burningion/skate-judge/capture/onboard.py

#!/usr/bin/env python3
# /// script
# requires-python = ">=3.10"
# dependencies = ["pyserial>=3.5"]
# ///
"""Record motion on SD or ESP32 flash; download after recording stops.

python3 capture/onboard.py record
python3 capture/onboard.py list
python3 capture/onboard.py download ID --output sessions/recovered
"""

from __future__ import annotations

import argparse
import io
from datetime import datetime, timezone
from http.client import IncompleteRead
import json
import math
import os
from pathlib import Path
import queue
import re
import sys
import threading
import time
from urllib.error import HTTPError, URLError
from urllib.parse import urlencode, urlsplit
from urllib.request import Request, urlopen
import uuid
import zlib

if __package__:
    from .onboard_log import import_log, read_packets
    from .session import ControlServer, append_json
else:
    from onboard_log import import_log, read_packets
    from session import ControlServer, append_json


def valid_id(identity):
    if not isinstance(identity, str) or not re.fullmatch(r"[a-f0-9]{32}", identity):
        raise ValueError("Expected a 32-character recording ID from the board's file list.")
    return identity


def checksum(path):
    crc = 0
    with Path(path).open("rb") as stream:
        for chunk in iter(lambda: stream.read(65536), b""):
            crc = zlib.crc32(chunk, crc)
    return f"{crc:08x}"


class BoardClient:
    def __init__(self, address="http://192.168.4.1", opener=urlopen):
        if "://" not in address:
            address = "http://" + address
        parsed = urlsplit(address)
        if parsed.scheme != "http" or not parsed.hostname or parsed.username or parsed.query or parsed.fragment:
            raise ValueError("Use the board's HTTP address, for example http://192.168.4.1.")
        self.address = address.rstrip("/")
        self.opener = opener
        self.lock = threading.Lock()

    def close(self):
        pass

    def request(self, route, params=None, post=False, timeout=2):
        url = self.address + route + ("?" + urlencode(params) if params else "")
        request = Request(url, data=b"" if post else None, method="POST" if post else "GET")
        try:
            with self.lock, self.opener(request, timeout=timeout) as response:
                return json.load(response)
        except HTTPError as error:
            try:
                message = json.load(error).get("error", str(error))
            except (ValueError, AttributeError):
                message = str(error)
            raise ValueError(message) from error
        except (URLError, TimeoutError, OSError) as error:
            raise OSError(f"Board connection unavailable: {error}") from error

    def download(self, identity, directory, storage=None):
        identity = valid_id(identity)
        params = {"id": identity}
        if storage is not None:
            if storage not in ("sd", "flash"):
                raise ValueError("Storage must be sd or flash.")
            params["storage"] = storage
        info = self.request("/file-info", params, timeout=120)
        backend = info.get("storage")
        if storage is not None and backend is None:
            raise ValueError("Install updated firmware to select a storage backend explicitly.")
        if backend is not None:
            if backend not in ("sd", "flash") or (storage and storage != backend):
                raise ValueError("Invalid or changed storage backend from board.")
            params["storage"] = backend
        if info.get("id") != identity or not isinstance(info.get("bytes"), int) or info["bytes"] <= 0:
            raise ValueError("Invalid file metadata from board.")
        directory = Path(directory)
        directory.mkdir(parents=True, exist_ok=True)
        target = directory / f"onboard-{identity}.bin"
        partial = target.with_suffix(".bin.part")
        if target.exists():
            if target.stat().st_size != info["bytes"] or checksum(target) != info["crc32"]:
                raise ValueError("An existing download differs from the board; it will not be overwritten.")
            return target
        last_error = None
        for _ in range(3):
            offset = partial.stat().st_size if partial.exists() else 0
            if offset > info["bytes"]:
                raise ValueError("Partial file is larger than the board recording; keep it and use a new directory.")
            if offset == info["bytes"]:
                break
            url = self.address + "/file?" + urlencode(dict(params, offset=offset))
            try:
                with self.lock, self.opener(url, timeout=5) as response:
                    if response.headers.get("X-Log-CRC32") != info["crc32"]:
                        raise ValueError("Recording changed during download.")
                    with partial.open("ab") as stream:
                        remaining = info["bytes"] - offset
                        while remaining:
                            chunk = response.read(min(65536, remaining))
                            if not chunk:
                                raise OSError("Download ended early.")
                            stream.write(chunk)
                            remaining -= len(chunk)
                        stream.flush()
                        os.fsync(stream.fileno())
                break
            except (OSError, URLError, IncompleteRead) as error:
                last_error = error
        if not partial.exists() or partial.stat().st_size != info["bytes"]:
            raise OSError(f"Download incomplete; partial data is saved at {partial}. Retry after reconnecting. {last_error}")
        if checksum(partial) != info["crc32"]:
            raise ValueError("Downloaded file checksum mismatch; retain it and download to a new directory.")
        packets, _, _ = read_packets(partial, allow_incomplete=True)
        if json.loads(packets[0][2]).get("id") != identity:
            raise ValueError("Downloaded recording ID does not match.")
        partial.rename(target)
        return target


class SerialResponse:
    def __init__(self, port, size, crc):
        self.port, self.remaining = port, size
        self.headers = {"X-Log-CRC32": crc}

    def read(self, size):
        data = self.port.read(min(size, self.remaining))
        if not data and self.remaining:
            raise OSError("USB download timed out; reconnect and retry.")
        self.remaining -= len(data)
        return data

    def __enter__(self):
        return self

    def __exit__(self, *args):
        pass


class SerialBoardClient(BoardClient):
    def __init__(self, address):
        import serial
        import serial.tools.list_ports

        port = address.removeprefix("serial:")
        if port == "auto":
            ports = [p.device for p in serial.tools.list_ports.comports() if p.vid in (0x303A, 0x239A)]
            if len(ports) != 1:
                raise ValueError(f"Expected one USB board, found {ports}. Pass --board serial:/dev/cu.usbmodem...")
            port = ports[0]
        self.port = serial.Serial(port, 115200, timeout=2, write_timeout=2)
        self.address = address
        self.lock = threading.Lock()
        self.opener = self._open

    def _open(self, request, timeout):
        url = request if isinstance(request, str) else request.full_url
        route = url[len(self.address):]
        method = "GET" if isinstance(request, str) else request.get_method()
        self.port.timeout = timeout
        self.port.write(f"{method} {route}\n".encode())
        deadline = time.monotonic() + timeout
        while time.monotonic() < deadline:
            # SD can retain far more recordings than flash; a files response
            # readily exceeds the old 4 KiB status-line bound.
            line = self.port.read_until(b"\n", size=1024 * 1024)
            if not line.startswith(b'{"status":'):
                continue  # Skip boot diagnostics before the protocol reply.
            reply = json.loads(line)
            if reply["status"] >= 400:
                raise ValueError(reply["body"].get("error", "Board request failed."))
            if "binary" in reply:
                return SerialResponse(self.port, reply["binary"], reply["crc32"])
            return io.BytesIO(json.dumps(reply["body"]).encode())
        raise OSError("USB board did not answer. Install the onboard logger firmware.")

    def close(self):
        self.port.close()


def board_client(address):
    return SerialBoardClient(address) if address.startswith("serial:") else BoardClient(address)


def wipe_recordings(client, storage=None):
    """Explicitly discard recordings on mounted board storage without downloading."""
    if storage not in (None, "sd", "flash"):
        raise ValueError("Storage must be sd or flash.")
    status = client.request("/status")
    if status.get("phase") not in ("idle", "saved", "fault"):
        raise ValueError("Stop recording and wait for the board to be idle before wiping recordings.")
    selection = {"storage": storage} if storage else None
    files = client.request("/files", selection, timeout=120)
    if not isinstance(files, list):
        raise ValueError("Invalid recording list from board.")
    # Validate the complete selection before deleting anything. Always pin the
    # backend: the same ID can exist independently on SD and internal flash.
    seen = set()
    for item in files:
        if not isinstance(item, dict):
            raise ValueError("Invalid recording entry from board.")
        identity = valid_id(item.get("id"))
        backend = item.get("storage")
        if backend not in ("sd", "flash") or (storage and backend != storage):
            raise ValueError("Missing or unexpected storage in board file list; check logger firmware.")
        size = item.get("bytes")
        if type(size) is not int or size < 0 or (backend, identity) in seen:
            raise ValueError("Invalid size or duplicate recording in board file list.")
        seen.add((backend, identity))

    deleted = 0
    reclaimed = 0
    try:
        for item in files:
            params = dict(id=item["id"], storage=item["storage"])
            info = client.request("/file-info", params, timeout=120)
            if (not isinstance(info, dict) or info.get("id") != item["id"]
                    or info.get("storage") != item["storage"] or info.get("bytes") != item["bytes"]
                    or not isinstance(info.get("crc32"), str)
                    or not re.fullmatch(r"[a-f0-9]{8}", info["crc32"])):
                raise ValueError("Recording metadata changed or is invalid; list recordings again.")
            # /delete rechecks this checksum, so a changed file cannot be
            # deleted using stale metadata. Wipe deliberately needs no backup.
            reply = client.request("/delete", dict(params, crc32=info["crc32"]), post=True, timeout=120)
            if not isinstance(reply, dict) or reply.get("deleted") is not True:
                raise ValueError("Board did not acknowledge recording deletion.")
            deleted += 1
            reclaimed += item["bytes"]
            print(f"Deleted {item['storage']}: {item['id']} ({item['bytes']} bytes).", flush=True)
        if client.request("/files", selection, timeout=120) != []:
            raise ValueError("Recordings remain on the selected storage; list them and retry.")
    except (ValueError, OSError) as error:
        raise ValueError(f"Wipe interrupted after {deleted} confirmed deletions. {error}") from error
    return dict(deleted=deleted, bytes=reclaimed, storage=storage or "all mounted")


def test_led(client, timeout=12):
    before = client.request("/status")
    if before.get("phase") not in ("idle", "saved", "fault"):
        raise ValueError("Stop recording and wait for the board to be idle before testing LEDs.")
    if "led_tests" not in before:
        raise ValueError("Install the updated logger with ./flash-feather.sh to use test-led.")
    print(f"Watch the stick on GPIO{before['led_pin']}: three one-second white pulses "
          f"({before['led_count']} pixels, {before['led_format']}, brightness {before['led_brightness']}/255).",
          flush=True)
    client.request("/test-led", post=True)
    deadline = time.monotonic() + timeout
    while time.monotonic() < deadline:
        status = client.request("/status")
        if status.get("boot_id") != before.get("boot_id"):
            raise ValueError("Board restarted during the LED test; completion is unconfirmed.")
        if status.get("led_tests", 0) > before["led_tests"]:
            print("LED commands completed; LEDs commanded off. Confirm visible light by eye.", flush=True)
            for key, label in (("led_test_battery_before_mv", "Battery before test"),
                               ("led_test_battery_on_mv", "Battery with LEDs commanded on")):
                value = status.get(key, -1)
                print(f"{label}: {value / 1000:.3f} V" if value >= 0 else f"{label}: unavailable")
            rmt_ready = status.get("led_test_rmt_ready", -1)
            print("GPIO LED transmitter attached and idle: " + {1: "yes", 0: "no"}.get(rmt_ready, "unavailable"))
            return status
        time.sleep(.25)
    raise ValueError("LED test completion was not acknowledged. Check board status.")


def healthy(status):
    return (status.get("phase") == "recording" and 180 <= status.get("accel_hz", 0) <= 230
            and 180 <= status.get("gyro_hz", 0) <= 230 and not status.get("error")
            and not status.get("io_errors") and not status.get("fifo_overruns")
            and status.get("zero_accel", 0) <= status.get("accel_samples", 0) * .25)


def battery_status(status, connected=True):
    """Only expose fresh gauge readings, including while the board is idle."""
    result = dict(state="unavailable", percent=None, voltage_mv=None)
    if not connected:
        return dict(result, state="offline")
    if "battery_available" not in status:
        return dict(result, state="unsupported")
    age = status.get("battery_age_ms")
    if type(age) not in (int, float) or not math.isfinite(age) or age < 0:
        return result
    if age > 15000:
        return dict(result, state="stale")
    percent, voltage = status.get("battery_percent"), status.get("battery_mv")
    if (status.get("battery_available") is not True
            or type(percent) not in (int, float) or not math.isfinite(percent) or not 0 <= percent <= 100
            or type(voltage) not in (int, float) or not math.isfinite(voltage) or not 2500 <= voltage <= 4500):
        return result
    return dict(state="ready", percent=percent, voltage_mv=voltage, age_ms=age)


def storage_budget(status, connected=True):
    """Approximate time for one log, using the firmware's storage stop limits.

    Older firmware supplies bytes/free_bytes too, so a reflash is not required.
    Reserve the entire async buffer while recording: free_bytes is sampled by
    the writer and may not account for the latest queued data yet.
    """
    backend = status.get("storage", "flash")
    result = dict(storage=backend, state="unavailable", remaining_s=None,
                  sd_fallback=connected and backend == "flash" and status.get("sd_ready") is False
                  and bool(status.get("storage_ready")),
                  free_bytes=None, bytes_per_second=None, rate_source=None, limit=None)
    if not connected:
        return dict(result, state="offline")
    free = status.get("free_bytes")
    if not status.get("storage_ready") or not isinstance(free, (int, float)) or not math.isfinite(free) or free < 0:
        return result
    result["free_bytes"] = free
    phase = status.get("phase")
    if phase in ("starting", "stopping", "testing_led", "fault"):
        return dict(result, state=phase)
    active = phase == "recording"
    if active and status.get("storage_recovering"):
        return dict(result, state="recovering")
    if phase not in ("idle", "saved", "recording") or status.get("error"):
        return result
    reserve = 32768  # RESERVE_BYTES in imu_logger.ino; protects closing the log.
    if not active and free < reserve + 65536:  # Firmware start preflight.
        return dict(result, state="full", remaining_s=0, limit="storage")
    rate, source = 5000, "typical"  # Conservative nominal 208 Hz + packet overhead.
    size = max(0, status.get("bytes", 0))
    start = status.get("started_us", 0)
    end = status.get("device_us", 0) if active else status.get("ended_us", 0)
    elapsed = max(0, end - start) / 1e6 if start else 0
    if elapsed >= 5 and size > 0 and (not active or healthy(status)):
        rate, source = size / elapsed, "measured"
    pending = max(0, status.get("storage_buffer_bytes", 0)) if active else 0
    available = max(0, free - reserve - pending)
    file_available = max(0, 0xffffffff - reserve - (size if active else 0))
    return dict(result, state="recording" if active else "ready",
                recoveries=status.get("storage_recoveries", 0) if active else 0,
                remaining_s=min(available, file_available) / rate,
                bytes_per_second=rate, rate_source=source,
                limit="file" if file_available < available else "storage")


class OnboardRecording:
    def __init__(self, client, path):
        self.client, self.path = client, Path(path)
        self.identity = None
        self.boot = None
        self.result = None
        self.operation = threading.Lock()
        self.remote = None
        self.message = "Connect to the board's Wi-Fi to prepare recording."
        self.downloading = False
        self.status_lock = threading.Lock()
        self.last_status_key = None
        self.last_status_saved = 0

    def status(self):
        with self.status_lock:
            status = self.client.request("/status")
            if status.get("protocol") != 1:
                raise ValueError("Install the onboard logger firmware first.")
            self.save_observation(status)
            if self.boot and status.get("boot_id") != self.boot:
                raise ValueError("Board restarted. The previous onboard log is retained; use the download command to recover it.")
            self.remote = status
            return status

    def save_observation(self, status):
        # Capture diagnostics while connected, before a fault prevents a footer
        # or a reboot clears RAM. Only sessions created by the recorder get logs.
        if not self.identity or not (self.path / "metadata.json").exists():
            return
        diagnostic = status.get("storage_diagnostics", {})
        key = tuple(status.get(k) for k in ("boot_id", "id", "phase", "error")) + (
            diagnostic.get("operation"), diagnostic.get("errno"), diagnostic.get("at_us"),
            status.get("storage_recovering"), status.get("storage_recoveries"), status.get("storage_recovery_attempts"))
        now = time.monotonic()
        changed = key != self.last_status_key
        if not changed and now - self.last_status_saved < 1:
            return
        observation = dict(status, observed_utc=datetime.now(timezone.utc).isoformat())
        append_json(self.path / "board_status.jsonl", observation)
        if (changed and status.get("error") and status.get("id") == self.identity
                and status.get("boot_id") == self.boot):
            temporary = self.path / "board_fault.json.tmp"
            with temporary.open("w") as stream:
                json.dump(observation, stream, indent=2)
                stream.flush()
                os.fsync(stream.fileno())
            temporary.replace(self.path / "board_fault.json")
        self.last_status_key, self.last_status_saved = key, now

    def prepare(self):
        with self.operation:
            if self.result:
                raise ValueError("This batch is saved. Start a new recorder command for the next batch.")
            status = self.status()
            if status["phase"] in ("recording", "starting", "stopping") and status.get("id") != self.identity:
                raise ValueError("The board already has an active recording. It will not be replaced.")
            if not status.get("storage_ready"):
                raise ValueError("Initialize the unused data partition first: python3 capture/onboard.py initialize")
            if not status.get("sensor_ready") or not status.get("led_enabled"):
                raise ValueError(status.get("error") or "Sensor and sync LED must be ready.")
            if self.identity is None:
                self.identity, self.boot = uuid.uuid4().hex, status["boot_id"]
                manifest = self.path / "metadata.json"
                meta = json.loads(manifest.read_text())
                meta.update(onboard_id=self.identity, onboard_address=self.client.address, boot_id=self.boot,
                            onboard_storage=status.get("storage", "flash"),
                            transport="onboard_" + status.get("storage", "flash"))
                temporary = manifest.with_suffix(".json.tmp")
                temporary.write_text(json.dumps(meta, indent=2) + "\n")
                temporary.replace(manifest)
            self.client.request("/start", {"id": self.identity}, post=True)
            deadline = time.monotonic() + 15
            while time.monotonic() < deadline:
                status = self.status()
                if status.get("id") == self.identity:
                    if status["phase"] in ("fault", "saved"):
                        raise ValueError(status.get("error") or "This recording has already stopped; download it.")
                    if healthy(status):
                        self.message = f"Recording to {status.get('storage', 'flash').upper()}. Wi-Fi carries controls and status only."
                        if status.get("storage_warning"):
                            self.message += " " + status["storage_warning"]
                        return dict(ready=True, id=self.identity)
                time.sleep(.1)
            raise ValueError("Sensor has not reached 180 Hz on both axes groups. Countdown cancelled; inspect board status.")

    def check_sync_ready(self):
        if self.result or self.downloading:
            raise ValueError("This batch is saving or already saved. Start a new recorder command for the next batch.")
        status = self.status()
        if not self.identity or status.get("id") != self.identity or not healthy(status):
            raise ValueError("Onboard recording is not healthy; sync cancelled.")
        return status

    def sync(self, marker):
        self.check_sync_ready()
        self.client.request("/sync", dict(id=self.identity, marker=marker), post=True)

    def finish(self):
        with self.operation:
            if self.result:
                return self.result
            if not self.identity:
                raise ValueError("No onboard recording was started. The video is saved separately.")
            self.downloading = True
            try:
                status = self.status()
                if status.get("id") != self.identity:
                    raise ValueError("Board recording changed. Recover the original recording with the download command.")
                self.message = "Stopping acquisition and closing the onboard file…"
                self.client.request("/stop", {"id": self.identity}, post=True)
                deadline = time.monotonic() + 30
                while time.monotonic() < deadline:
                    status = self.status()
                    if status["phase"] in ("saved", "fault"):
                        break
                    time.sleep(.1)
                else:
                    raise OSError("Board has not acknowledged stopping. Reconnect and retry; its file remains onboard.")
                # Retain errors from final fsync/close even if the subsequent
                # download fails and is recovered by a later CLI invocation.
                manifest = self.path / "metadata.json"
                meta = json.loads(manifest.read_text())
                meta["onboard_stop_error"] = status.get("error", "")
                meta["onboard_stop_status"] = status
                temporary = manifest.with_suffix(".json.tmp")
                temporary.write_text(json.dumps(meta, indent=2) + "\n")
                temporary.replace(manifest)
                self.message = "Downloading and verifying the raw onboard file…"
                raw = self.client.download(self.identity, self.path)
                meta = import_log(raw, self.path, allow_incomplete=True, stop_error=status.get("error", ""))
                quality = meta["onboard_quality"]
                self.result = dict(saved=True, raw_file=raw.name, samples=meta["samples"], quality=quality)
                self.message = f"Saved {meta['samples']:,} samples at {quality['measured_hz']:.1f} Hz. Original retained onboard."
                if quality.get("storage_recoveries"):
                    self.message += f" Recovered SD interruptions: {quality['storage_recoveries']}."
                if not quality["usable"]:
                    self.message += " Quality issues: " + ", ".join(quality["issues"])
                return self.result
            except (ValueError, OSError) as error:
                self.message = f"Board data needs recovery: {error} Use Retry board download or the download command."
                raise
            finally:
                self.downloading = False


def record(args):
    path = args.output or Path("sessions") / (datetime.now().strftime("%Y%m%d-%H%M%S-") + uuid.uuid4().hex[:6])
    path.mkdir(parents=True, exist_ok=False)
    (path / "metadata.json").write_text(json.dumps(dict(schema=1, transport="onboard_flash", synthetic=False,
        created_utc=datetime.now(timezone.utc).isoformat(), rider=args.rider, board=args.board_name,
        samples=0, duration_s=0, onboard_address=args.board), indent=2) + "\n")
    recording = OnboardRecording(board_client(args.board), path)
    commands = queue.Queue()
    control = ControlServer(commands, path, args.port, onboard=recording)
    phase, message, remaining = "ready", "Record video + sync starts video before the countdown.", None
    deadline, marker = 0, 0

    def terminal():
        for line in sys.stdin:
            commands.put(line.strip())
    threading.Thread(target=terminal, daemon=True).start()
    print(f"Onboard capture controls: {control.url}\nSession: {path}\nCommands: status, finish, quit.\nQuitting the laptop does not stop the board or erase its log.", flush=True)
    try:
        while True:
            countdown_handled = False
            try:
                remote = recording.status()
                connected = True
            except (ValueError, OSError) as error:
                remote, connected = recording.remote or {}, False
                recording.message = f"{error} Onboard capture does not depend on Wi-Fi. Reconnect to stop/download."
            now = time.monotonic()
            while not commands.empty():
                command = commands.get_nowait()
                if command == "quit":
                    if control.videos.active:
                        print("Stop & save video first. Board data remains onboard.", flush=True)
                    else:
                        return
                elif command == "status":
                    print(json.dumps(remote, indent=2), flush=True)
                elif command == "finish":
                    try:
                        recording.finish()
                    except (ValueError, OSError) as error:
                        print(error, file=sys.stderr, flush=True)
                elif command == "countdown":
                    countdown_handled = True
                    try:
                        # The status at the top of this iteration may predate
                        # prepare() reaching a healthy acquisition rate.
                        remote = recording.check_sync_ready()
                        connected = True
                    except (ValueError, OSError) as error:
                        remote, connected = recording.remote or {}, False
                        phase, remaining, message = "error", None, str(error)
                        continue
                    now = time.monotonic()
                    phase, remaining, deadline = "countdown", 3, now + 3
                    message = "Video and onboard data are recording. Sync in 3…"
            if phase == "countdown":
                if not connected or not healthy(remote):
                    phase, remaining, message = "error", None, "Countdown cancelled: board status unavailable or unhealthy."
                else:
                    remaining = max(0, math.ceil(deadline - now))
                    message = f"Sync in {remaining}…"
                    if not remaining:
                        marker += 1
                        try:
                            recording.sync(marker)
                            phase, remaining, deadline = "waiting", None, time.monotonic() + 3
                            message = "Waiting for the recorded LED timestamp…"
                        except (OSError, ValueError) as error:
                            phase, message = "error", str(error)
            elif phase == "waiting":
                if connected and remote.get("id") == recording.identity and remote.get("sync_id") == marker:
                    phase, message = "done", f"Flash recorded onboard — sync {marker}."
                elif now > deadline:
                    phase, message = "error", "No flash acknowledgement. The onboard log is retained; reconnect and retry sync."
            active = remote.get("phase") == "recording"
            if connected and not recording.downloading and not recording.result:
                if active:
                    recording.message = (f"{remote.get('storage', 'flash').upper()} · Accel {remote.get('accel_hz', 0):.1f} Hz · "
                        f"Gyro {remote.get('gyro_hz', 0):.1f} Hz · {remote.get('free_bytes', 0) / (1024 * 1024):.1f} MiB free · "
                        f"Read retries {remote.get('bus_retries', 0)} · Read errors {remote.get('io_errors', 0)} · FIFO overruns {remote.get('fifo_overruns', 0)}")
                elif remote.get("error"):
                    recording.message = remote["error"]
                elif not remote.get("storage_ready"):
                    recording.message = "Initialize unused storage with: python3 capture/onboard.py initialize"
                else:
                    recording.message = f"Board ready. Motion will be recorded to {remote.get('storage', 'flash').upper()} when you start video + sync."
                if remote.get("storage_warning"):
                    recording.message += " " + remote["storage_warning"]
            ready = (connected and not recording.result and not recording.downloading
                     and remote.get("sensor_ready") and remote.get("storage_ready")
                     and remote.get("led_enabled") and remote.get("phase") in ("idle", "saved", "recording")
                     and (not active or (remote.get("id") == recording.identity and healthy(remote))))
            own_recording = bool(recording.identity and remote.get("id") == recording.identity)
            elapsed = max(0, ((remote.get("ended_us") or remote.get("device_us", 0)) - remote.get("started_us", 0)) / 1e6) if own_recording and remote.get("started_us") else 0
            control.publish_status(dict(onboard=True, session=path.name, session_path=str(path.resolve()),
                    synthetic=False, samples=remote.get("accel_samples", 0) if own_recording else 0, duration_s=elapsed,
                    fresh=bool(ready), can_sync=bool(ready and phase not in ("countdown", "waiting")),
                    phase=phase, remaining=remaining, message=message, board_message=recording.message,
                    storage_budget=storage_budget(remote, connected),
                    battery=battery_status(remote, connected),
                    can_download=bool(recording.identity and not recording.result and not recording.downloading)),
                    countdown_handled=countdown_handled)
            time.sleep(.2)
    except KeyboardInterrupt:
        pass
    finally:
        control.close()
        recording.client.close()
        if recording.identity and not recording.result:
            print(f"Board recording retained: {recording.identity}\nRecover: python3 capture/onboard.py download {recording.identity} --output {path}", flush=True)


def main():
    parser = argparse.ArgumentParser(description=__doc__)
    parser.add_argument("--board", default="http://192.168.4.1")
    sub = parser.add_subparsers(dest="command", required=True)
    rec = sub.add_parser("record")
    rec.add_argument("--output", type=Path)
    rec.add_argument("--port", type=int, default=0)
    rec.add_argument("--rider", default="rider-01")
    rec.add_argument("--board-name", default="deck-01")
    sub.add_parser("status")
    sub.add_parser("check-sensor", help="Reinitialize the IMU while idle, after checking its cable")
    sub.add_parser("test-led", help="Three one-second LED pulses while idle; does not create a recording")
    sub.add_parser("initialize", help="Initialize a blank data partition; refuses to erase existing data")
    listing = sub.add_parser("list")
    listing.add_argument("--storage", choices=("sd", "flash"))
    down = sub.add_parser("download")
    down.add_argument("id")
    down.add_argument("--storage", choices=("sd", "flash"))
    down.add_argument("--output", type=Path, required=True)
    down.add_argument("--allow-incomplete", action="store_true")
    delete = sub.add_parser("delete", help="Delete one verified downloaded recording from the board")
    delete.add_argument("id")
    delete.add_argument("--storage", choices=("sd", "flash"))
    delete.add_argument("--downloaded", type=Path, required=True)
    wipe = sub.add_parser("wipe", help="Permanently delete all board recordings without downloading",
                          description="Delete all recordings on mounted SD and internal flash. "
                                      "Laptop session files, firmware, and settings are kept.")
    wipe.add_argument("--storage", choices=("sd", "flash"), help="Limit deletion to one storage medium")
    wipe.add_argument("--yes", action="store_true", required=True,
                      help="Confirm permanent deletion, including recordings never downloaded")
    stop = sub.add_parser("stop")
    stop.add_argument("id")
    convert = sub.add_parser("import")
    convert.add_argument("file", type=Path)
    convert.add_argument("--output", type=Path, required=True)
    convert.add_argument("--allow-incomplete", action="store_true")
    args = parser.parse_args()
    client = None
    try:
        client = board_client(args.board) if args.command not in ("record", "import") else None
        if args.command == "record":
            record(args)
        elif args.command == "status":
            print(json.dumps(client.request("/status"), indent=2))
        elif args.command == "check-sensor":
            client.request("/check-sensor", post=True)
            time.sleep(.5)
            print(json.dumps(client.request("/status"), indent=2))
        elif args.command == "test-led":
            test_led(client)
        elif args.command == "initialize":
            print(json.dumps(client.request("/initialize", post=True, timeout=15), indent=2))
        elif args.command == "list":
            print(json.dumps(client.request("/files", {"storage": args.storage} if args.storage else None), indent=2))
        elif args.command == "wipe":
            print(json.dumps(wipe_recordings(client, args.storage)))
        elif args.command == "stop":
            print(json.dumps(client.request("/stop", {"id": valid_id(args.id)}, post=True), indent=2))
        elif args.command in ("download", "import"):
            if args.command == "download":
                raw = client.download(valid_id(args.id), args.output, storage=args.storage)
                print(f"Verified raw file: {raw}. Original retained onboard.")
            else:
                raw = args.file
            meta = import_log(raw, args.output, args.allow_incomplete)
            print(json.dumps(meta["onboard_quality"], indent=2))
        elif args.command == "delete":
            identity = valid_id(args.id)
            packets, _, _ = read_packets(args.downloaded, allow_incomplete=True)
            if json.loads(packets[0][2]).get("id") != identity:
                raise ValueError("The downloaded file has a different recording ID.")
            params = dict(id=identity, crc32=checksum(args.downloaded))
            if args.storage:
                params["storage"] = args.storage
            print(json.dumps(client.request("/delete", params, post=True, timeout=120)))
    except (ValueError, OSError, ImportError) as error:
        parser.exit(1, f"Error: {error}\n")
    finally:
        if client:
            client.close()


if __name__ == "__main__":
    main()
